klemetsson/stratux-zero/cam/stratux-zero/rev1/pdf/Stratux-Zero-GKO.pdf

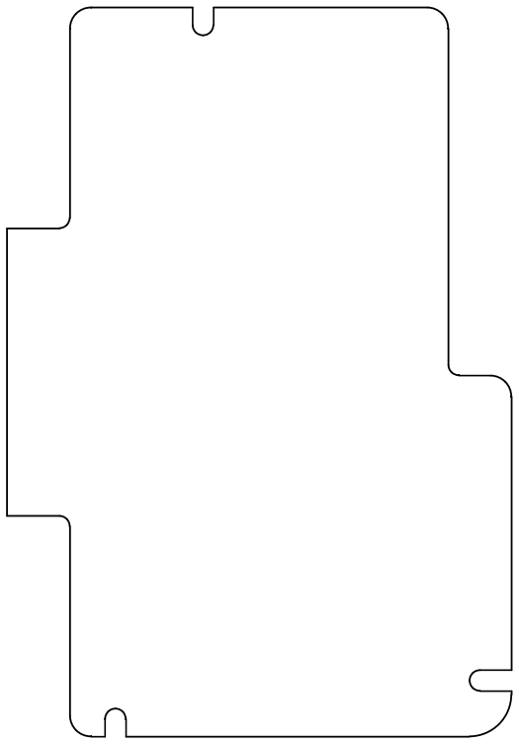
[picture p4: figure]
