klemetsson/stratux-zero/cam/stratux-zero/rev1/pdf/Stratux-Zero-G2L.pdf

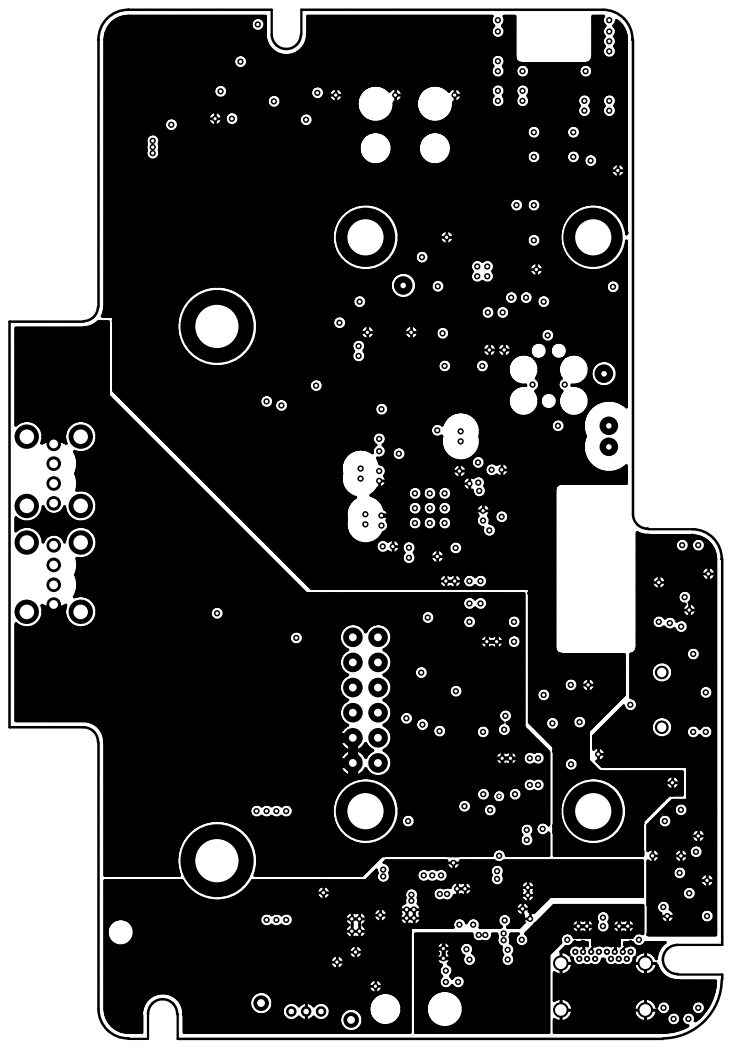
[picture p14: page 1]
