klemetsson/stratux-zero/cam/stratux-zero/rev1/pdf/Stratux-Zero-G3L.pdf

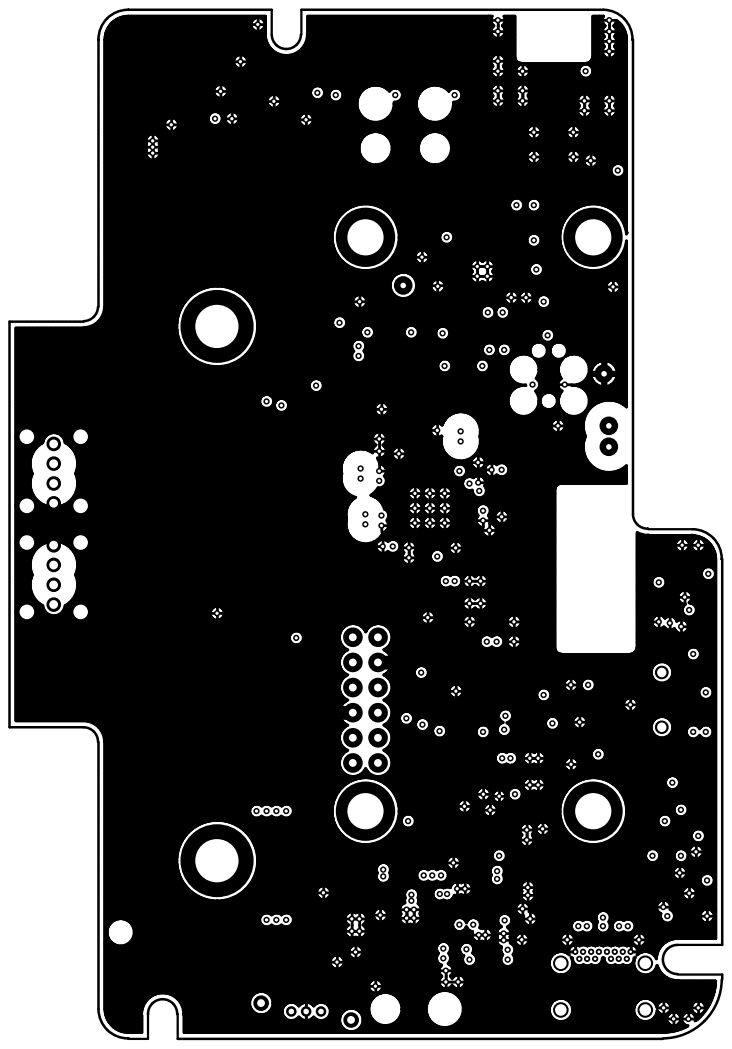
[picture p15: page 1]
