klemetsson/stratux-zero/cam/stratux-zero/rev1/pdf/Stratux-Zero-GBL.pdf

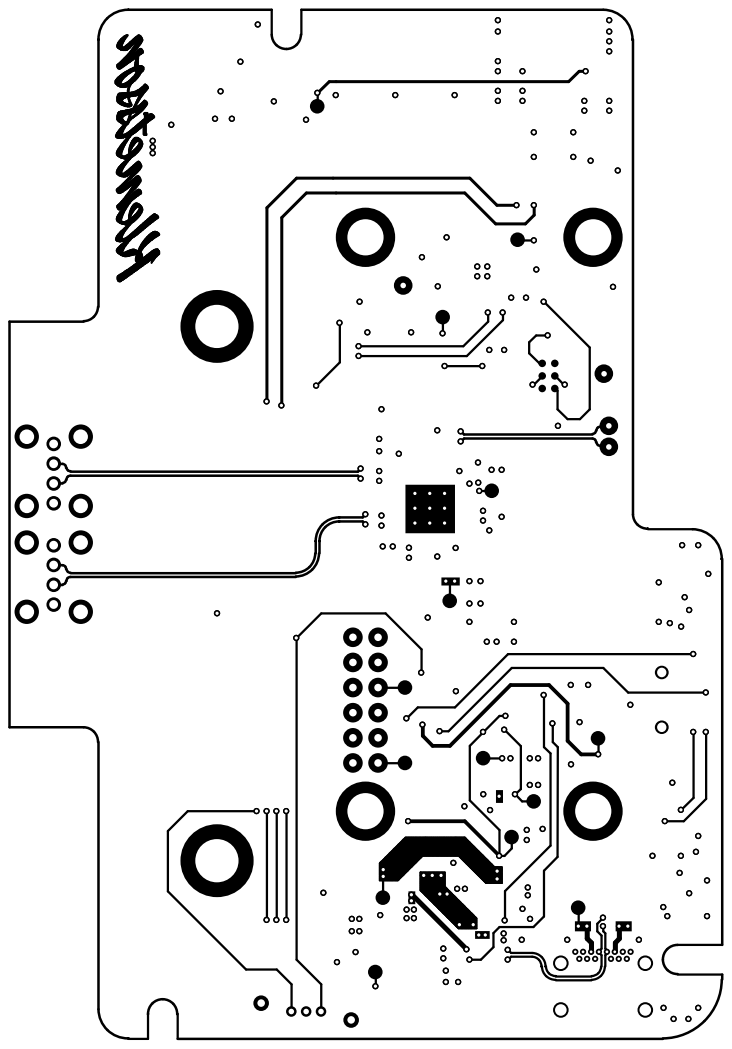
[picture p16: page 1]
