klemetsson/stratux-zero/cam/stratux-zero/rev1/pdf/Stratux-Zero-GTL.pdf

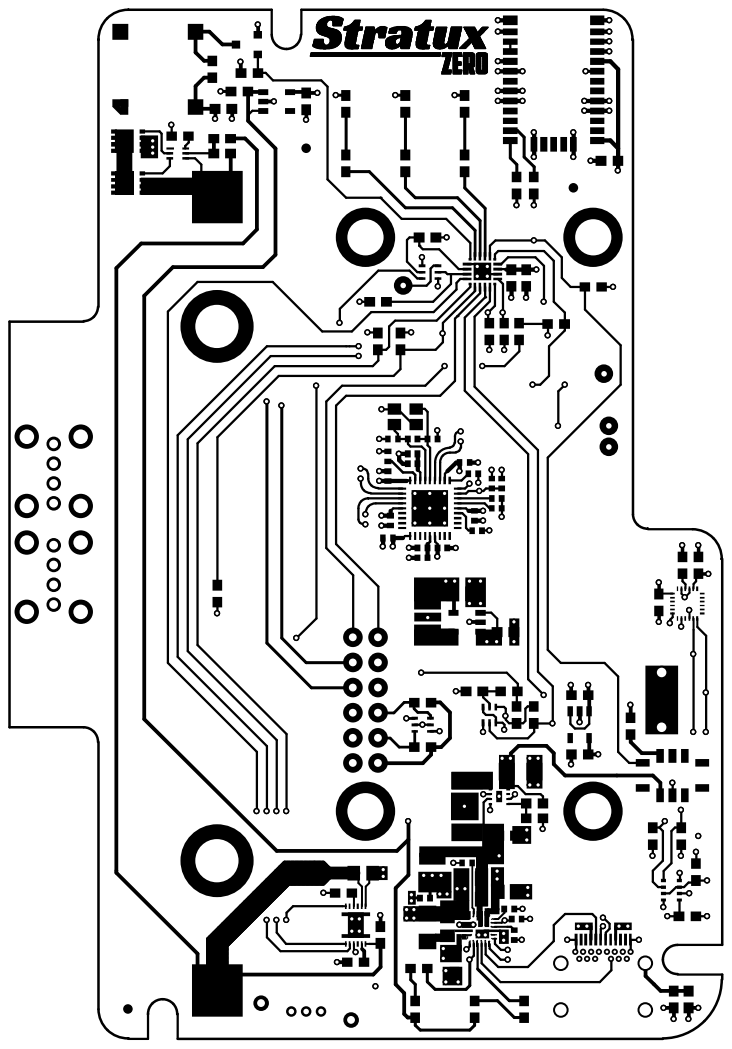
[picture p17: page 1]
