klemetsson/stratux-zero/cam/stratux-zero/rev1/pdf/Stratux-Zero-GTO.pdf

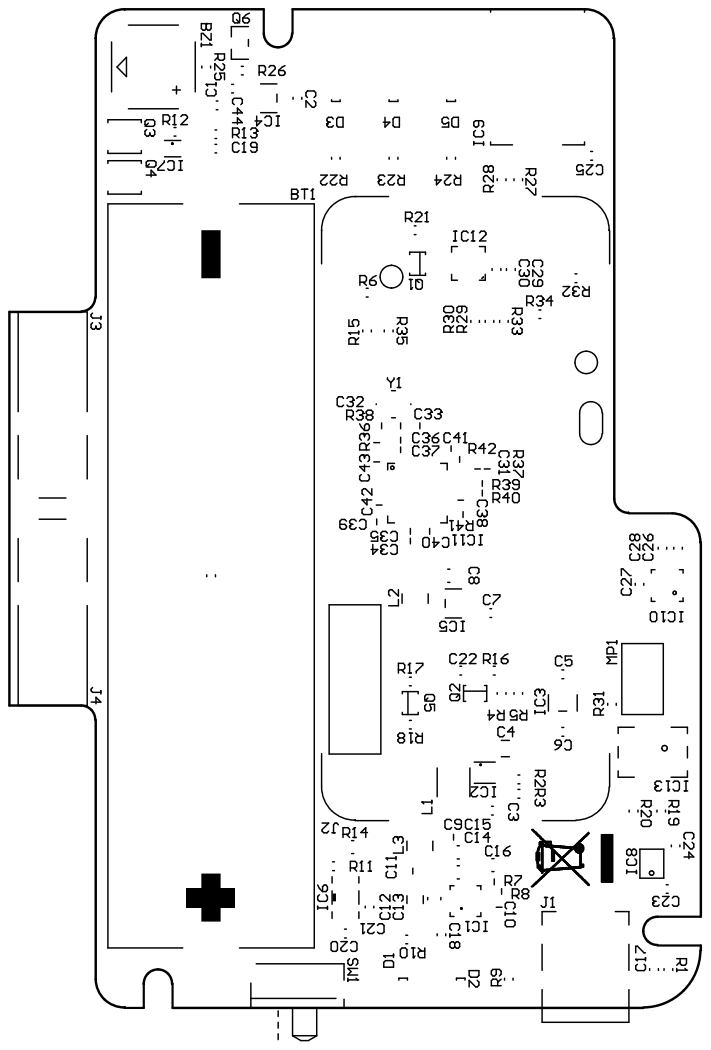
[picture p18: page 1]
