klemetsson/stratux-zero/cam/stratux-zero/rev1/pdf/Stratux-Zero-GTP.pdf

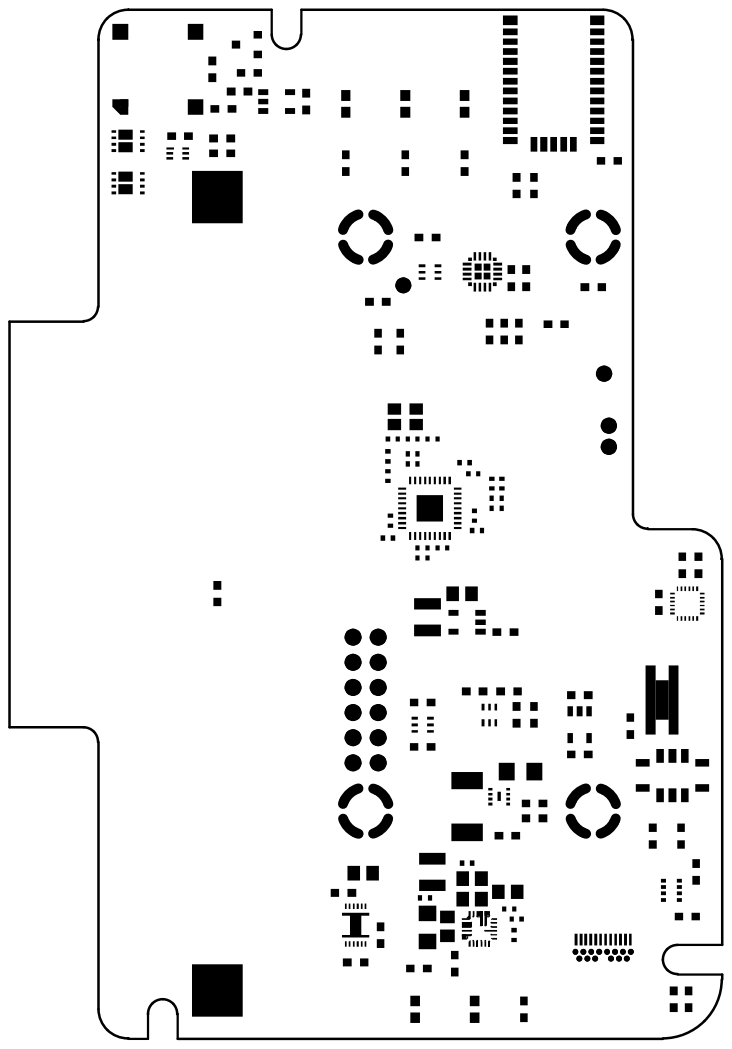
[picture p19: page 1]
